calliconfused/GitLack/Pictures/20200127_221329.jpg

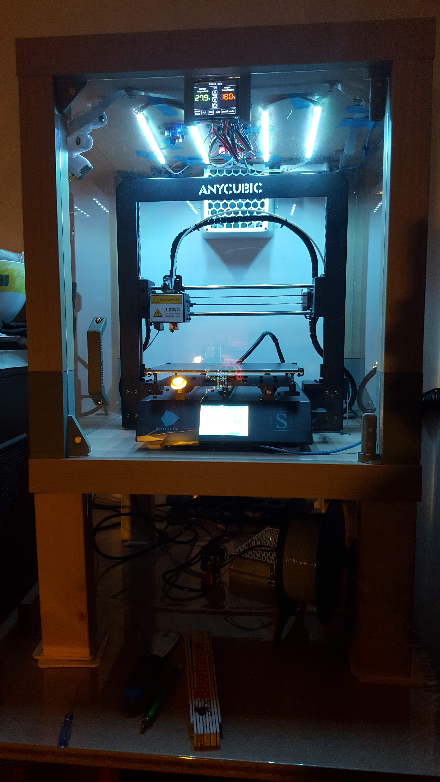
Pictures/20200127_221329.jpg
