calliconfused/GitLack/GitLack_MASTER/DSEG7REGULAR40.h

/*
 * This is a font for seven segment digits - size 40 px
 * 
 * Created by http://oleddisplay.squix.ch/ Consider a donation
 * In case of problems make sure that you are using the font file with the correct version!
 */ 

const uint8_t DSEG7REGULAR40Bitmaps[] PROGMEM = {

  // Bitmap Data:
  0x00, // ' '
  0x00, // '!'
  0xFF,0xD0,0x0A,0x01,0x40,0x28,0x05,0x00,0xA0,0x14,0x02,0x80,0x50,0x0A,0x01,0x40,0x28,0x05,0x00,0xA0,0x14,0x02,0x80,0x50,0x0A,0x01,0x40,0x28,0x05,0x00,0xA0,0x14,0x02,0x80,0x5F,0xF8, // '"'
  0xFF,0xD0,0x0A,0x01,0x40,0x28,0x05,0x00,0xA0,0x14,0x02,0x80,0x50,0x0A,0x01,0x40,0x28,0x05,0x00,0xA0,0x14,0x02,0x80,0x50,0x0A,0x01,0x40,0x28,0x05,0x00,0xA0,0x14,0x02,0x80,0x5F,0xF8, // '#'
  0xFF,0xD0,0x0A,0x01,0x40,0x28,0x05,0x00,0xA0,0x14,0x02,0x80,0x50,0x0A,0x01,0x40,0x28,0x05,0x00,0xA0,0x14,0x02,0x80,0x50,0x0A,0x01,0x40,0x28,0x05,0x00,0xA0,0x14,0x02,0x80,0x5F,0xF8, // '$'
  0xFF,0xD0,0x0A,0x01,0x40,0x28,0x05,0x00,0xA0,0x14,0x02,0x80,0x50,0x0A,0x01,0x40,0x28,0x05,0x00,0xA0,0x14,0x02,0x80,0x50,0x0A,0x01,0x40,0x28,0x05,0x00,0xA0,0x14,0x02,0x80,0x5F,0xF8, // '%'
  0xFF,0xD0,0x0A,0x01,0x40,0x28,0x05,0x00,0xA0,0x14,0x02,0x80,0x50,0x0A,0x01,0x40,0x28,0x05,0x00,0xA0,0x14,0x02,0x80,0x50,0x0A,0x01,0x40,0x28,0x05,0x00,0xA0,0x14,0x02,0x80,0x5F,0xF8, // '&'
  0xFF,0xD0,0x0A,0x01,0x40,0x28,0x05,0x00,0xA0,0x14,0x02,0x80,0x50,0x0A,0x01,0x40,0x28,0x05,0x00,0xA0,0x14,0x02,0x80,0x50,0x0A,0x01,0x40,0x28,0x05,0x00,0xA0,0x14,0x02,0x80,0x5F,0xF8, // '''
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
    {   956,  26,  40,  34,    4,  -40 }, // '5'
    {  1086,  26,  40,  34,    4,  -40 }, // '6'
    {  1216,  26,  37,  34,    4,  -40 }, // '7'
    {  1337,  26,  40,  34,    4,  -40 }, // '8'
    {  1467,  26,  40,  34,    4,  -40 }, // '9'
    {  1597,  23,  37,  34,    4,  -40 }, // 'f'
    {  1704,  26,  22,  34,    4,  -22 } // 'o'
 
};
const GFXfont DSEG7REGULAR40 PROGMEM = {
(uint8_t  *)DSEG7REGULAR40Bitmaps,(GFXglyph *)DSEG7REGULAR40Glyphs,0x20, 0x7E, 44};
