calliconfused/GitLack/GitLack_MASTER/OpenSansCondensed16pt.h

/*
 * This is a regular font instead of the stupid pixed font
 * 
 * Created by http://oleddisplay.squix.ch/ Consider a donation
 * In case of problems make sure that you are using the font file with the correct version!
 */ 
 
const uint8_t Open_Sans_Condensed_Bold_16Bitmaps[] PROGMEM = {

	// Bitmap Data:
	0x00, // ' '
	0xDB,0x6D,0xB6,0x1B,0x60, // '!'
	0xDB,0x6D,0xB6, // '"'
	0x1B,0x04,0x81,0x21,0xFE,0x7F,0x8D,0x83,0x63,0xFC,0xFF,0x09,0x02,0x41,0xB0, // '#'
	0x21,0xEF,0xAA,0xA3,0x87,0x0E,0x28,0xAF,0xBC,0x20,0x80, // '$'
	0x71,0x83,0xCC,0x16,0x41,0xB6,0x05,0xA0,0x3F,0x71,0xDF,0x80,0xB4,0x0D,0xB0,0x4D,0x06,0x78,0x31,0xC0, // '%'
	0x3C,0x0F,0x06,0x61,0xB0,0x3C,0x0E,0x07,0x99,0xBC,0xEF,0x19,0xC7,0xF0,0xEE, // '&'
	0xDB,0x60, // '''
	0x63,0x31,0x8C,0x63,0x18,0xC6,0x31,0x8C,0x31,0x80, // '('
	0x63,0x0C,0x63,0x18,0xC6,0x31,0x8C,0x63,0x31,0x80, // ')'
	0x10,0x10,0xFE,0x38,0x28,0x6C, // '*'
	0x20,0x82,0x3E,0xF8,0x82,0x00, // '+'
	0x66,0x6C, // ','
	0xEE, // '-'
	0xDB,0x00, // '.'
	0x0C,0x30,0x60,0xC3,0x06,0x0C,0x18,0x60,0xC1,0x86,0x00, // '/'
	0x73,0xED,0xB6,0xDB,0x6D,0xB6,0xDB,0x6F,0x9C, // '0'
	0x39,0xEF,0xAE,0x38,0xE3,0x8E,0x38,0xE3,0x8E, // '1'
	0x38,0xF9,0x30,0x60,0xC3,0x86,0x1C,0x30,0xC1,0xF3,0xE0, // '2'
	0x78,0xF9,0x30,0x60,0xC7,0x0F,0x06,0x0D,0x1B,0xF3,0xC0, // '3'
	0x1C,0x1C,0x1C,0x3C,0x2C,0x6C,0x6C,0xCC,0xFE,0xFE,0x0C,0x0C, // '4'
	0xFB,0xEC,0x30,0xF3,0xE1,0x86,0x18,0x6F,0xBC, // '5'
	0x39,0xEC,0x30,0xB3,0xED,0xB6,0xDB,0x6F,0x9C, // '6'
	0xFB,0xE1,0x86,0x18,0xC3,0x0C,0x61,0x86,0x38, // '7'
	0x73,0xED,0xB6,0xD9,0xC7,0x36,0xDB,0x6F,0x9C, // '8'
	0x73,0xED,0xB6,0xDB,0x6F,0xBE,0x18,0x6F,0x38, // '9'
	0xDB,0x00,0x36,0xC0, // ':'
	0x66,0x60,0x00,0x06,0x66,0xC0, // ';'
	0x00,0x23,0xB8,0xC3,0x83,0x82,0x00, // '<'
	0xFB,0xE0,0x3E,0xF8, // '='
	0x02,0x0E,0x0E,0x18,0xEE,0x20,0x00, // '>'
	0x79,0xF0,0x70,0x61,0x87,0x0C,0x18,0x00,0x61,0xC1,0x80, // '?'
	0x1F,0x07,0x71,0x83,0x67,0x6D,0xA5,0x24,0xAC,0x95,0x92,0x97,0xDB,0xB3,0x00,0x39,0x81,0xF0, // '@'
	0x1C,0x07,0x03,0x60,0xD8,0x36,0x0D,0x86,0x31,0xFC,0x7F,0x18,0xCE,0x3B,0x06, // 'A'
	0xF9,0xFB,0x36,0x6C,0xDF,0x3F,0x66,0xCD,0x9B,0xF7,0xC0, // 'B'
	0x38,0xF3,0x86,0x0C,0x18,0x30,0x60,0xC1,0xC1,0xE1,0xC0, // 'C'
	0xF8,0xFC,0xCE,0xC6,0xC6,0xC6,0xC6,0xC6,0xC6,0xCE,0xFC,0xF8, // 'D'
	0xFB,0xEC,0x30,0xC3,0xEF,0xB0,0xC3,0x0F,0xBE, // 'E'
	0xFD,0xFB,0x06,0x0C,0x1F,0x3E,0x60,0xC1,0x83,0x06,0x00, // 'F'
	0x3E,0x7E,0xE2,0xC0,0xC0,0xCE,0xCE,0xC6,0xC6,0xE6,0x7E,0x3E, // 'G'
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
};
const GFXglyph Open_Sans_Condensed_Bold_16Glyphs[] PROGMEM = {
// bitmapOffset, width, height, xAdvance, xOffset, yOffset
	  {     0,   1,   1,   5,    0,    0 }, // ' '
	  {     1,   3,  12,   5,    1,  -12 }, // '!'
	  {     6,   6,   4,   8,    1,  -12 }, // '"'
	  {     9,  10,  12,  10,    0,  -12 }, // '#'
	  {    24,   6,  14,   8,    1,  -13 }, // '$'
	  {    35,  13,  12,  13,    0,  -12 }, // '%'
	  {    55,  10,  12,  10,    0,  -12 }, // '&'
	  {    70,   3,   4,   5,    1,  -12 }, // '''
	  {    72,   5,  15,   6,    1,  -12 }, // '('
	  {    82,   5,  15,   6,    0,  -12 }, // ')'
	  {    92,   8,   6,   8,    0,  -13 }, // '*'
	  {    98,   6,   7,   8,    1,   -9 }, // '+'
	  {   104,   4,   4,   5,    0,   -2 }, // ','
	  {   106,   4,   2,   6,    1,   -5 }, // '-'
	  {   107,   3,   3,   5,    1,   -3 }, // '.'
	  {   109,   7,  12,   7,    0,  -12 }, // '/'
	  {   120,   6,  12,   8,    1,  -12 }, // '0'
	  {   129,   6,  12,   8,    1,  -12 }, // '1'
	  {   138,   7,  12,   8,    0,  -12 }, // '2'
	  {   149,   7,  12,   8,    0,  -12 }, // '3'
	  {   160,   8,  12,   8,    0,  -12 }, // '4'
	  {   172,   6,  12,   8,    1,  -12 }, // '5'
	  {   181,   6,  12,   8,    1,  -12 }, // '6'
	  {   190,   6,  12,   8,    1,  -12 }, // '7'
	  {   199,   6,  12,   8,    1,  -12 }, // '8'
	  {   208,   6,  12,   8,    1,  -12 }, // '9'
	  {   217,   3,   9,   5,    1,   -9 }, // ':'
	  {   221,   4,  11,   5,    0,   -9 }, // ';'
	  {   227,   6,   9,   8,    1,  -10 }, // '<'
	  {   234,   6,   5,   8,    1,   -8 }, // '='
	  {   238,   6,   9,   8,    1,  -10 }, // '>'
	  {   245,   7,  12,   7,    0,  -12 }, // '?'
	  {   256,  11,  13,  13,    1,  -12 }, // '@'
	  {   274,  10,  12,  10,    0,  -12 }, // 'A'
	  {   289,   7,  12,   9,    1,  -12 }, // 'B'
	  {   300,   7,  12,   8,    1,  -12 }, // 'C'
	  {   311,   8,  12,  10,    1,  -12 }, // 'D'
	  {   323,   6,  12,   8,    1,  -12 }, // 'E'
	  {   332,   7,  12,   8,    1,  -12 }, // 'F'
	  {   343,   8,  12,  10,    1,  -12 }, // 'G'
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
};
const GFXfont Open_Sans_Condensed_Bold_16 PROGMEM = {
(uint8_t  *)Open_Sans_Condensed_Bold_16Bitmaps,(GFXglyph *)Open_Sans_Condensed_Bold_16Glyphs,0x20, 0x7E, 23};
